j-crowley/TR_EMG/LTspice Sims/2ndOrderBPF.asc

C1: cap; 1µ
C2: cap; 1µ
C3: cap; 1µ
C4: cap; 1µ
R1: res; 320
R2: res; 320
R3: res; 1
R4: res; 1k
R5: res; 16k
R6: res; 1k
R7: res; 1k
R8: res; 16k
R9: res; 1k
U1: opamp
U3: opamp
V1: voltage; ""; AC 0.001
Named nets: 0
.lib opamp.sub
.ac lin 2000 1 1000
