j-crowley/TR_EMG/LTspice Sims/2ndOrderBSF.asc

C1: cap; 0.1µ
C2: cap; 0.1µ
R1: res; 29k
R2: res; 24.5k
R3: res; 1k
R4: res; 1k
R5: res; 1k
R6: res; 1
U1: opamp
U2: opamp
U3: opamp
V1: voltage; ""; AC 0.001
Named nets: 0
.lib opamp.sub
.ac lin 1000 1 100
