j-crowley/TR_EMG/LTspice Sims/AllFiltersRev2.asc

C1: cap; 0.1µ
C2: cap; 0.1µ
C3: cap; 0.1µ
C4: cap; 0.1µ
C5: cap; 0.1µ
C6: cap; 0.1µ
C7: cap; 0.1µ
C8: cap; 0.1µ
R1: res; 3.3k
R2: res; 3.3k
R3: res; 1k
R4: res; 1k
R5: res; 26.7k
R6: res; 26.7k
R7: res; 13k
R8: res; 330k
R9: res; 330k
R10: res; 150
R11: res; 100k
U1: opamp
U2: opamp
U3: opamp
V1: voltage; ""; AC 5
Named nets: 0
.ac lin 10000 1 1000
bandpass 5-500 hz
.lib opamp.sub
notch 60 hz
